androda/BlueSCSI/hw/Desktop_50Pin/F4_SMD_V1_1/TopOfPCB.PNG

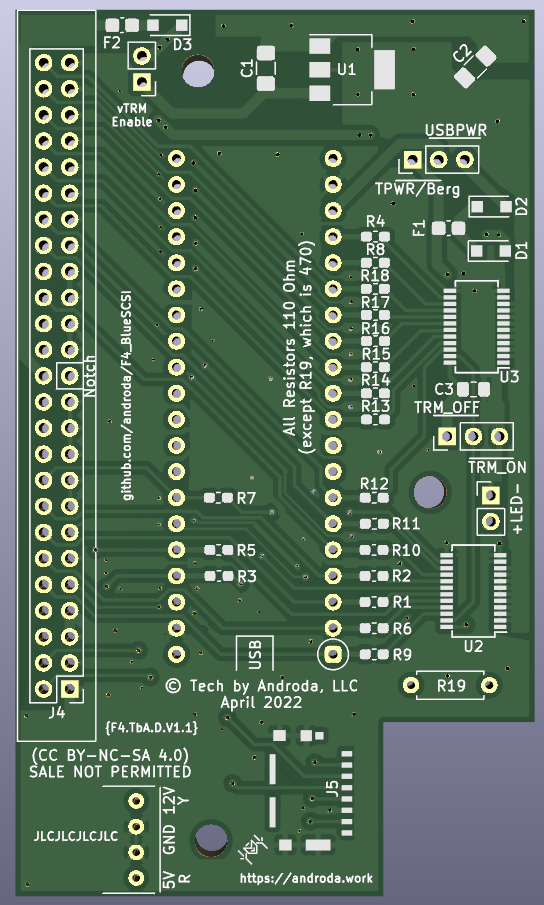
hw/Desktop_50Pin/F4_SMD_V1_1/TopOfPCB.PNG
