androda/BlueSCSI/hw/Desktop_50Pin/F4Lite_THTV1.1/TopOfPCB.PNG

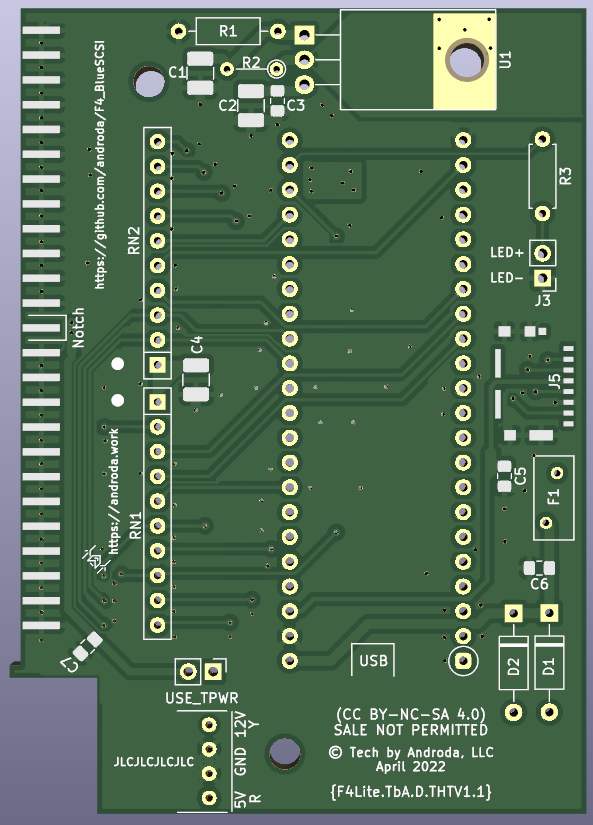
hw/Desktop_50Pin/F4Lite_THTV1.1/TopOfPCB.PNG
