androda/BlueSCSI/hw/Desktop_50Pin/XCVR_F4Lite_SMD_V1/TopOfPCB.PNG

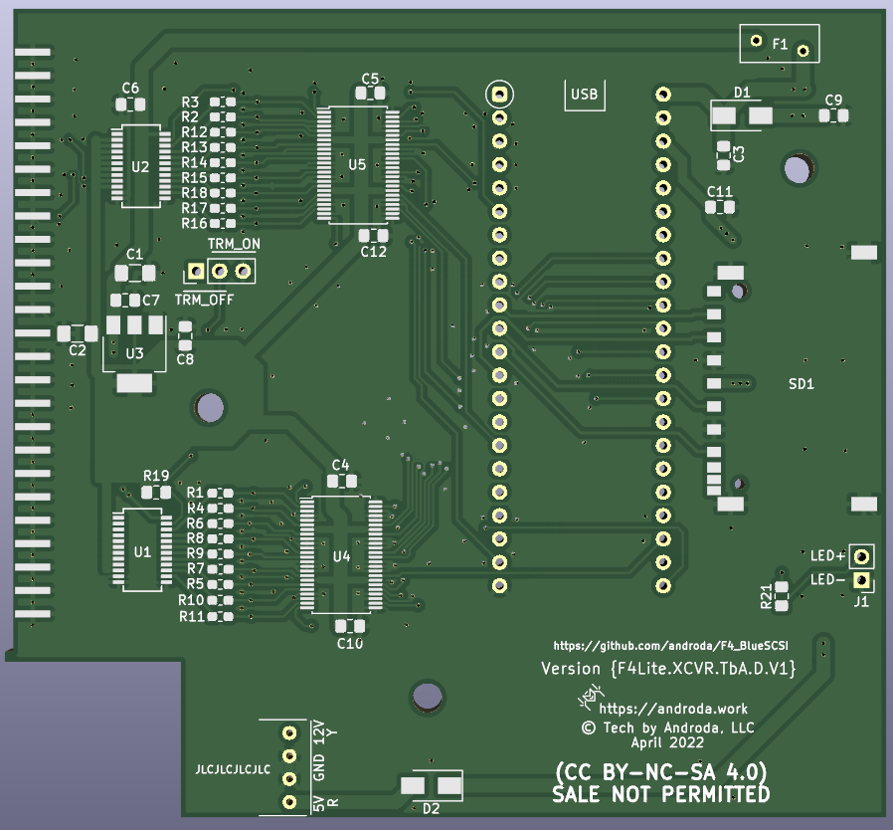
hw/Desktop_50Pin/XCVR_F4Lite_SMD_V1/TopOfPCB.PNG
