androda/BlueSCSI/hw/PowerBook/PowerBook_F4_THTV1/TopOfPCB.PNG

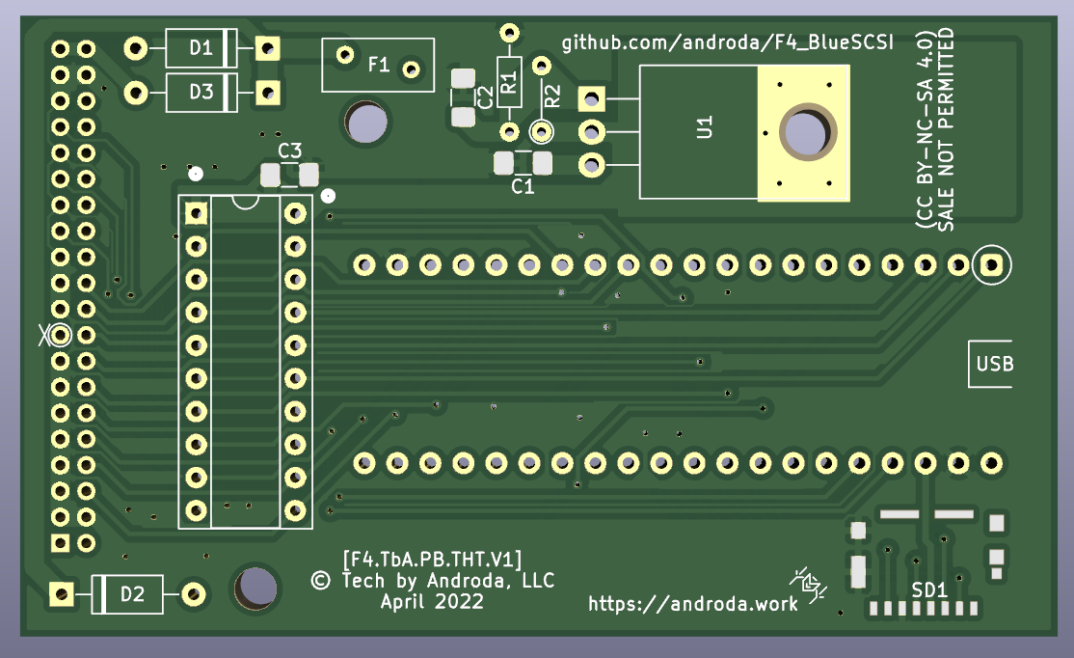
hw/PowerBook/PowerBook_F4_THTV1/TopOfPCB.PNG
