androda/BlueSCSI/hw/PowerBook/PowerBook_F4Lite_THTV1.2/TopOfPCB.PNG

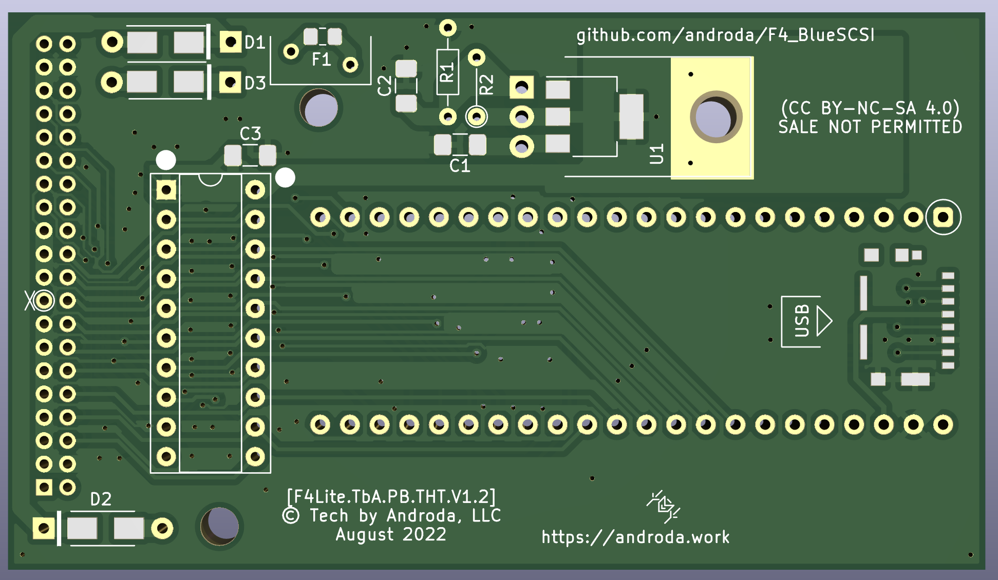
hw/PowerBook/PowerBook_F4Lite_THTV1.2/TopOfPCB.PNG
